Arpan-dell/smart-laundry-system/code/laundry_system/secrets.example.h

// Template for laundry_system.ino. Copy to secrets.h and fill in.
// Microcontrollers have no environment variables, so secrets live here instead of in the sketch.
#pragma once

// Telegram bot token from @BotFather.
#define TELEGRAM_BOT_TOKEN "123456789:AA...your-bot-token"

// Chat ID that receives the messages.
#define TELEGRAM_CHAT_ID "123456789"

// Default pickup address (personal data).
#define PICKUP_ADDRESS "Your pickup address"
